leejooheonn/EDES301/python/HydrationHelper/kid_cat.gif

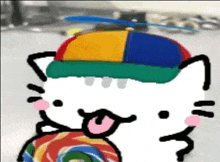
python/HydrationHelper/kid_cat.gif
