leejooheonn/EDES301/python/HydrationHelper/cat_tear_1.png

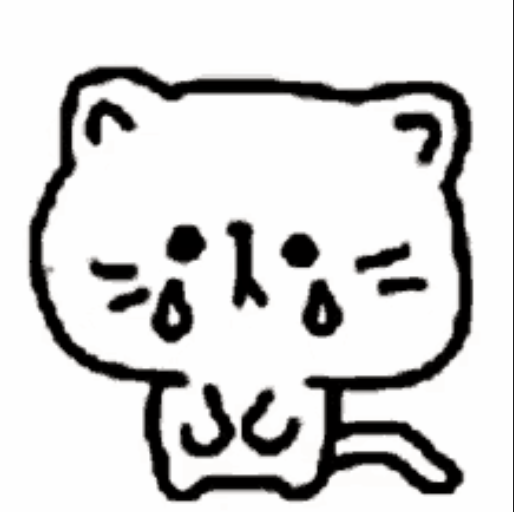
python/HydrationHelper/cat_tear_1.png
