leejooheonn/EDES301/python/HydrationHelper/cat_tear_2.png

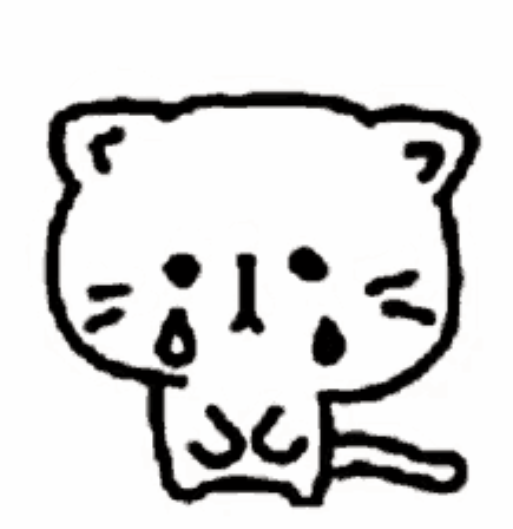
python/HydrationHelper/cat_tear_2.png
