leejooheonn/EDES301/python/HydrationHelper/cat_tear_3.png

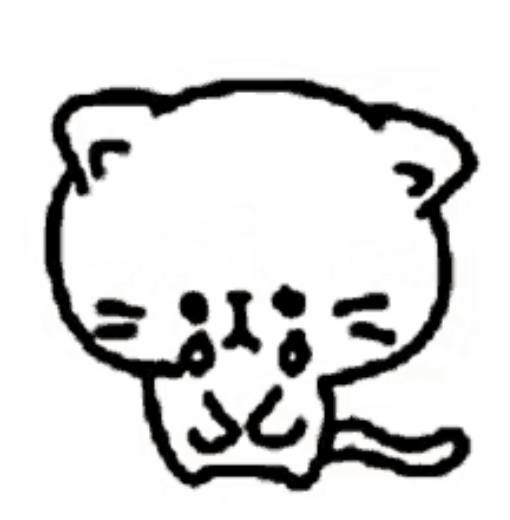
python/HydrationHelper/cat_tear_3.png
