leejooheonn/EDES301/python/HydrationHelper/exasperated_cat.webp

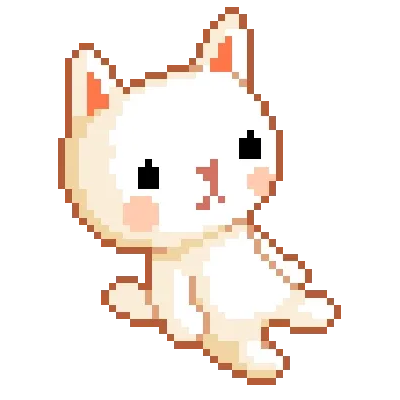
python/HydrationHelper/exasperated_cat.webp
