leejooheonn/EDES301/python/HydrationHelper/jumping_cat_1.jpeg

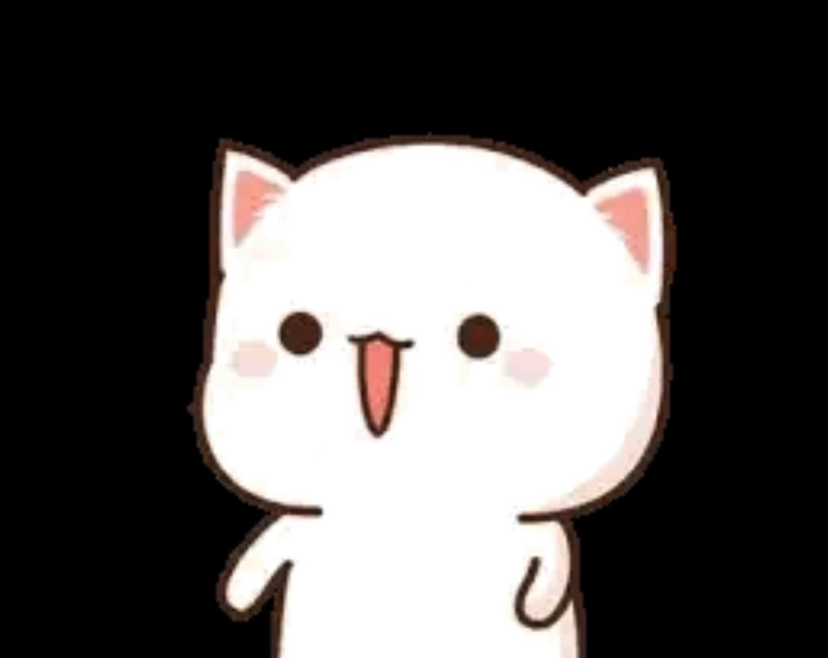
python/HydrationHelper/jumping_cat_1.jpeg
