leejooheonn/EDES301/python/HydrationHelper/jumping_cat_2.jpeg

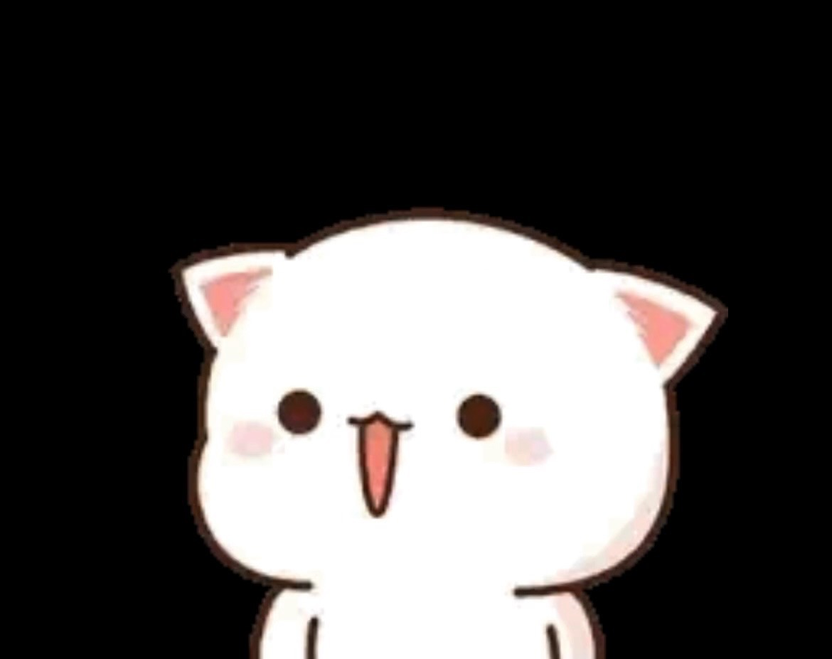
python/HydrationHelper/jumping_cat_2.jpeg
