leejooheonn/EDES301/python/HydrationHelper/jumping_cat_4.jpeg

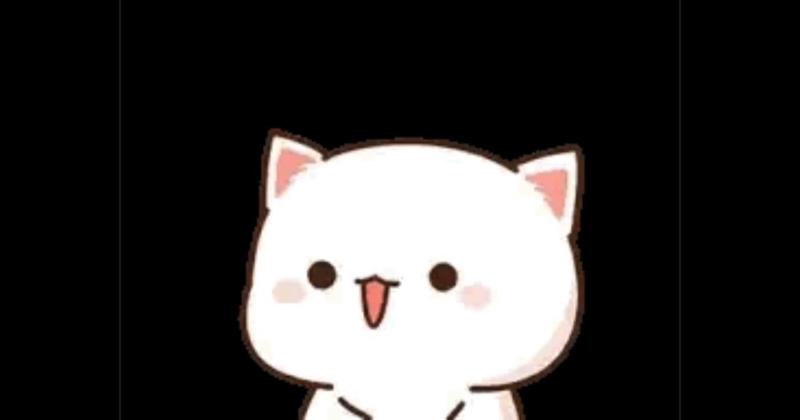
python/HydrationHelper/jumping_cat_4.jpeg
