leejooheonn/EDES301/python/HydrationHelper/jumping_cat_5.jpeg

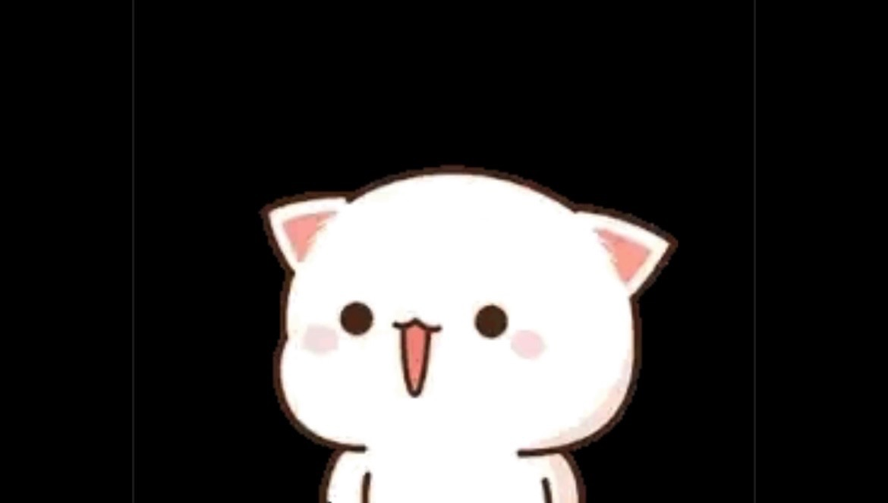
python/HydrationHelper/jumping_cat_5.jpeg
