leejooheonn/EDES301/python/HydrationHelper/jumping_cat_6.jpeg

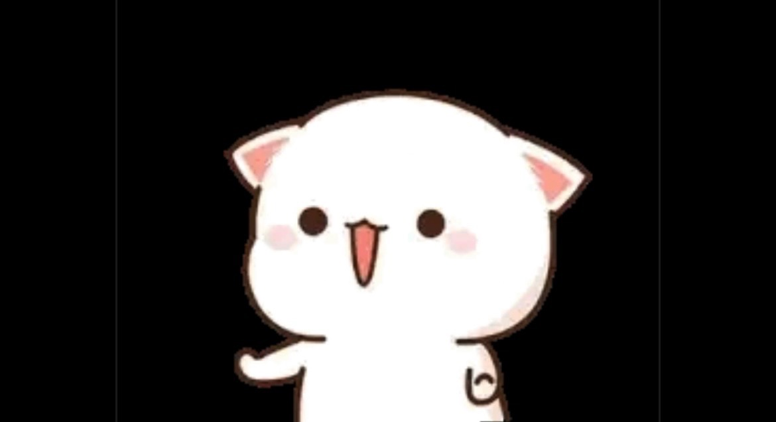
python/HydrationHelper/jumping_cat_6.jpeg
