leejooheonn/EDES301/python/HydrationHelper/jumping_cat_7.jpeg

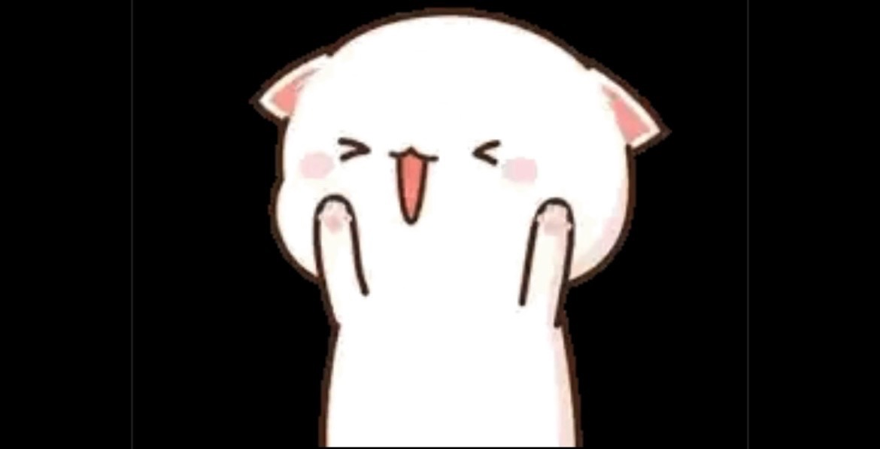
python/HydrationHelper/jumping_cat_7.jpeg
