leejooheonn/EDES301/python/HydrationHelper/running_cat_2.jpeg

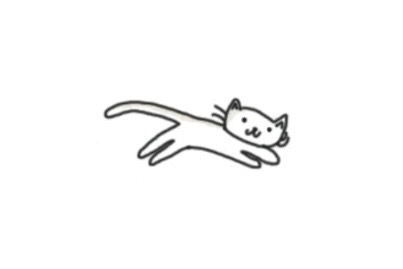
python/HydrationHelper/running_cat_2.jpeg
