leejooheonn/EDES301/python/HydrationHelper/running_cat_3.jpeg

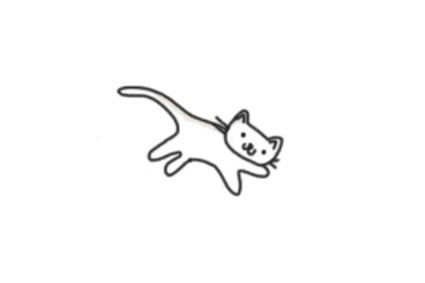
python/HydrationHelper/running_cat_3.jpeg
