leejooheonn/EDES301/python/HydrationHelper/running_cat_4.jpeg

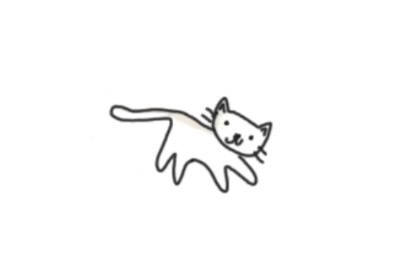
python/HydrationHelper/running_cat_4.jpeg
