leejooheonn/EDES301/python/HydrationHelper/running_cat_5.jpeg

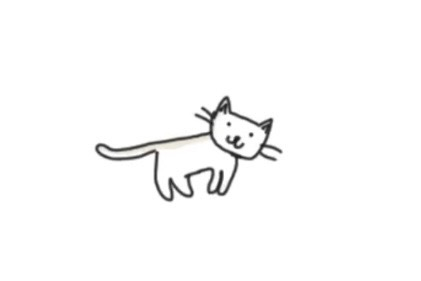
python/HydrationHelper/running_cat_5.jpeg
