leejooheonn/EDES301/python/HydrationHelper/Screenshot 2026-04-22 at 9.08.17 PM.png

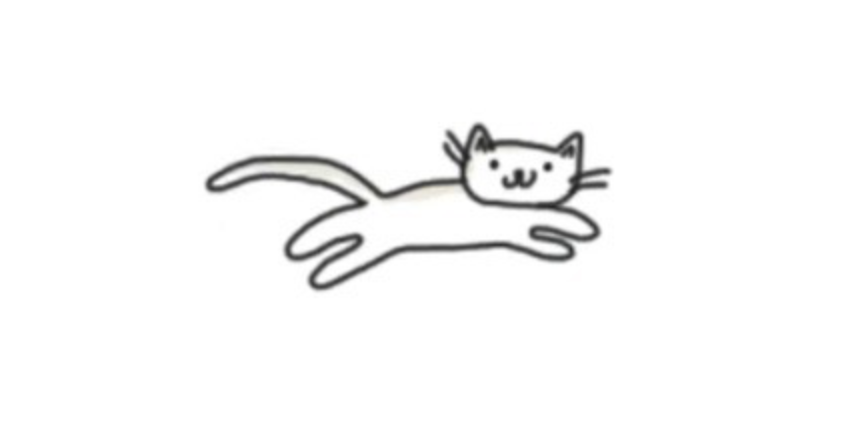
python/HydrationHelper/Screenshot 2026-04-22 at 9.08.17 PM.png
