leejooheonn/EDES301/project_02/MFG/bill_of_materials.png

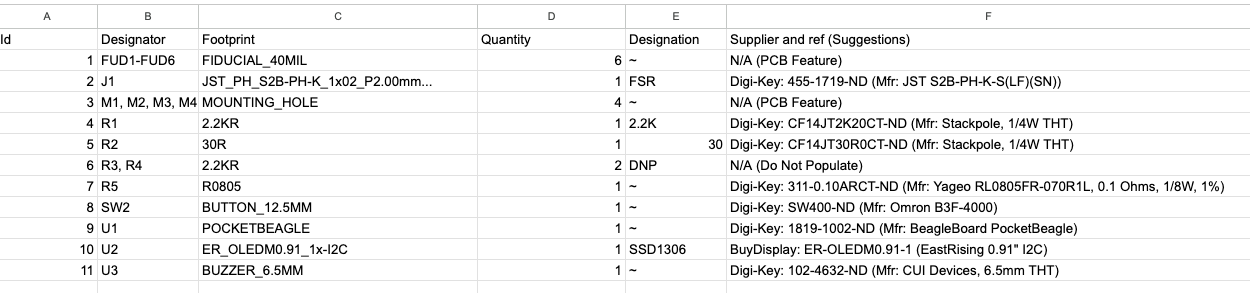
project_02/MFG/bill_of_materials.png
