leejooheonn/EDES301/project_02/MFG/BOM_updated.png

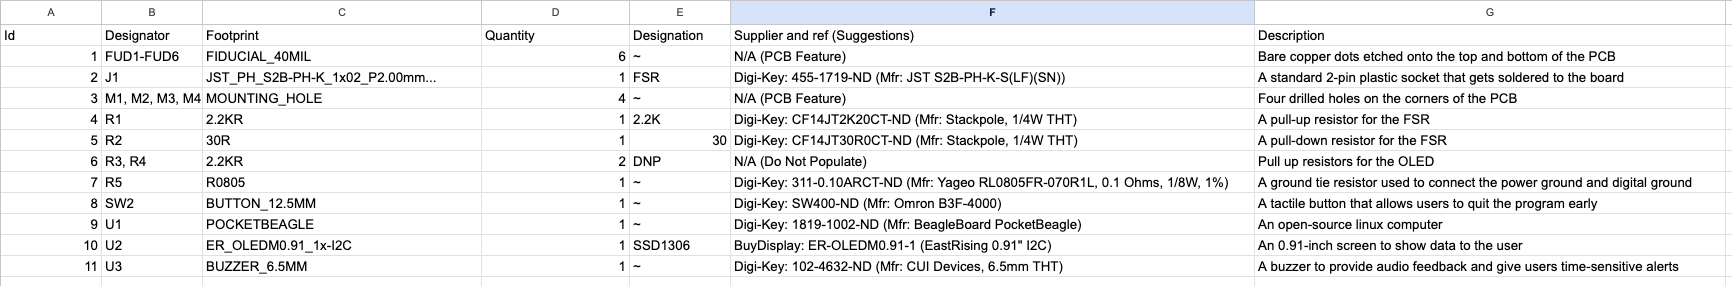
project_02/MFG/BOM_updated.png
